SerikovAleksey/GPS-Tracker/Инструкция/1.jpg

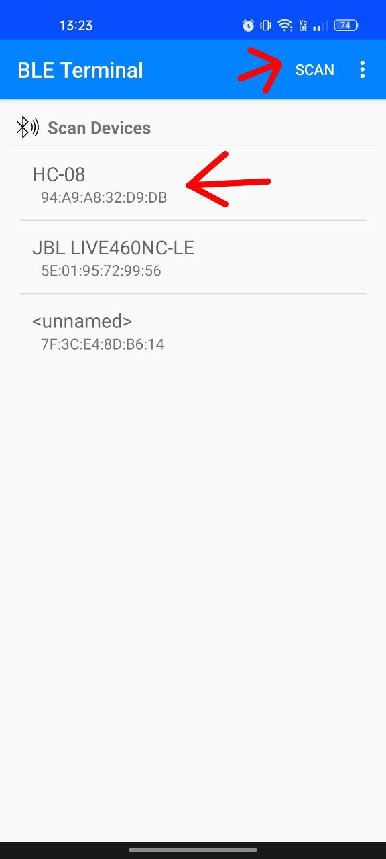
Инструкция/1.jpg
