SerikovAleksey/GPS-Tracker/Инструкция/2.jpg

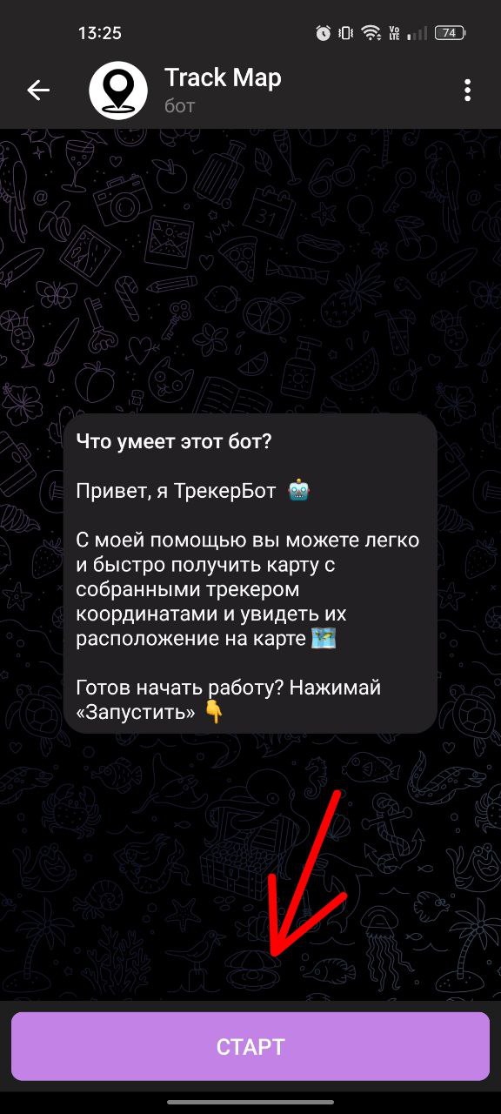
Инструкция/2.jpg
