SerikovAleksey/GPS-Tracker/Инструкция/4.jpg

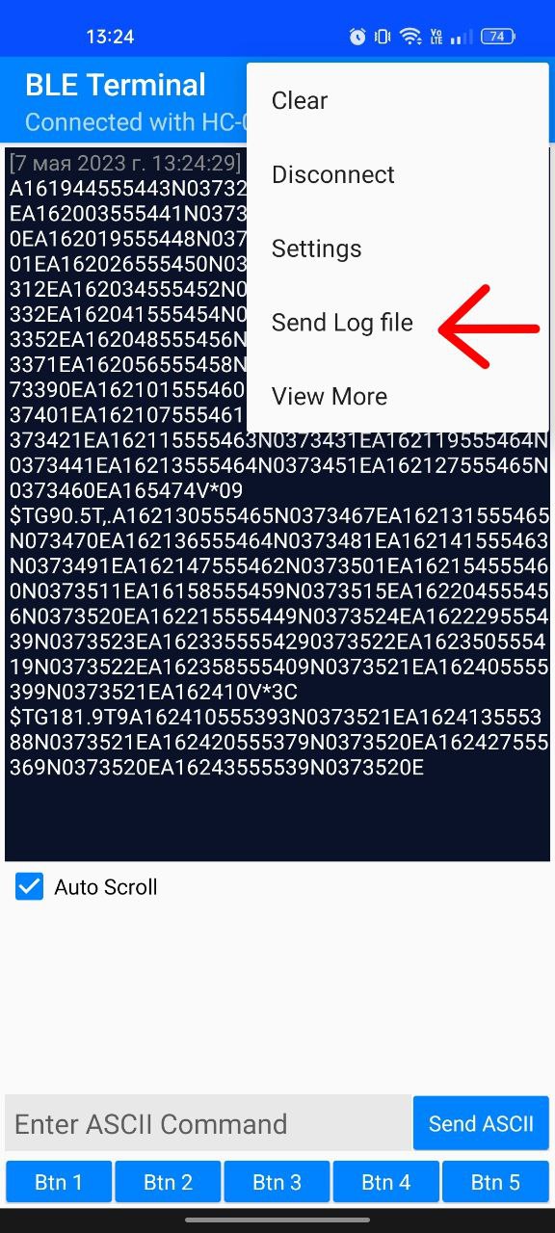
Инструкция/4.jpg
