SerikovAleksey/GPS-Tracker/Инструкция/5.jpg

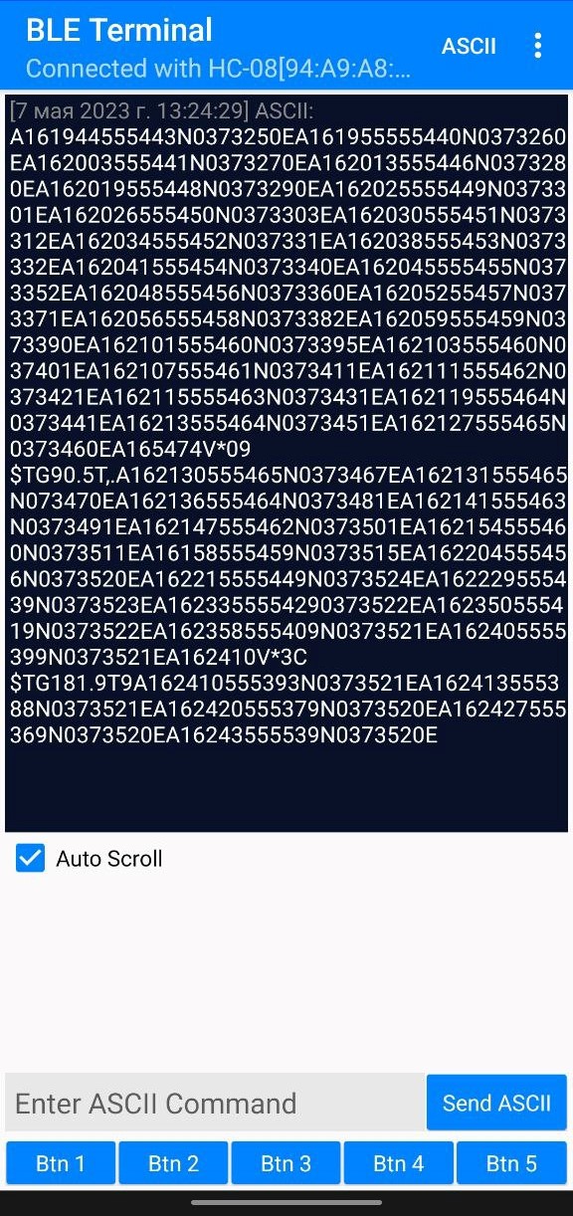
Инструкция/5.jpg
