SerikovAleksey/GPS-Tracker/Инструкция/6.jpg

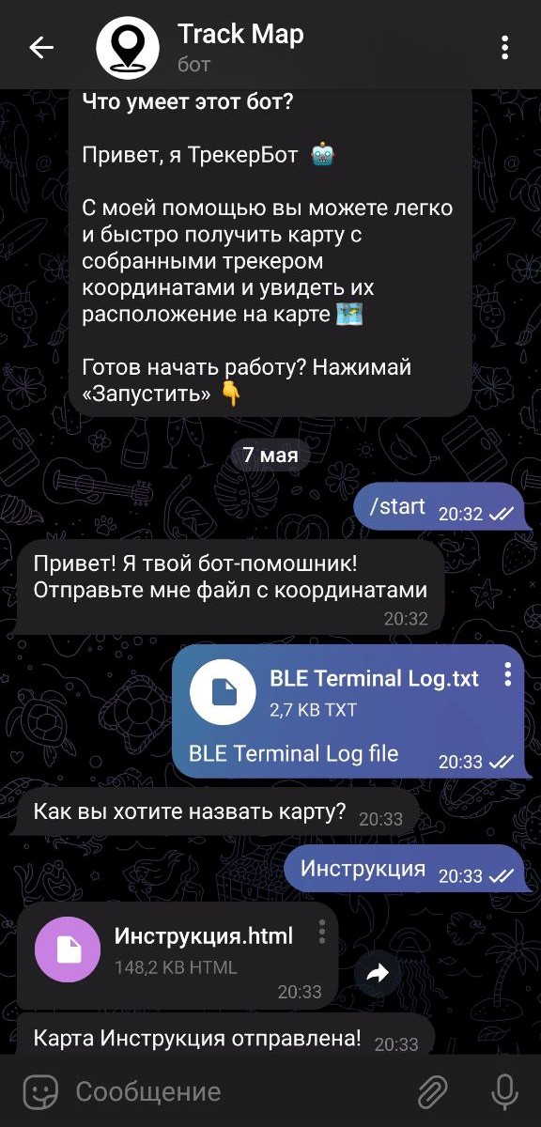
Инструкция/6.jpg
