SerikovAleksey/GPS-Tracker/Инструкция/трекер.png

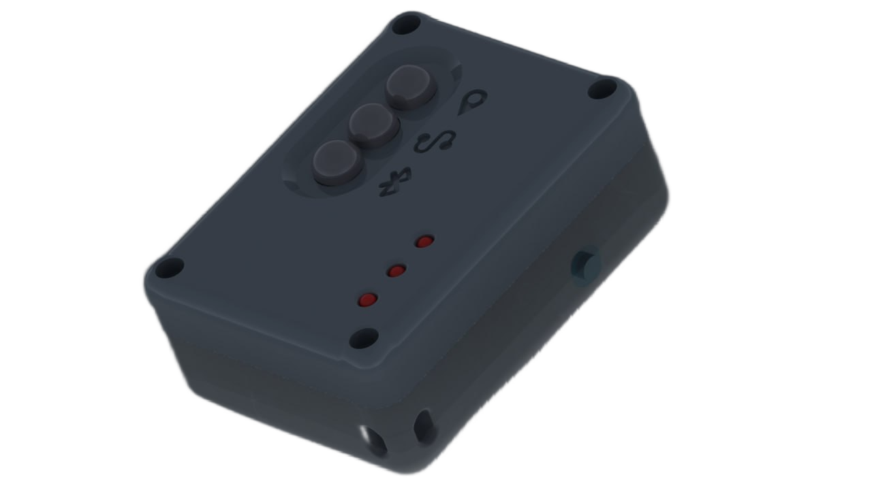
Инструкция/трекер.png
