SerikovAleksey/GPS-Tracker/Фото/photo_2023-04-14_23-05-25.jpg

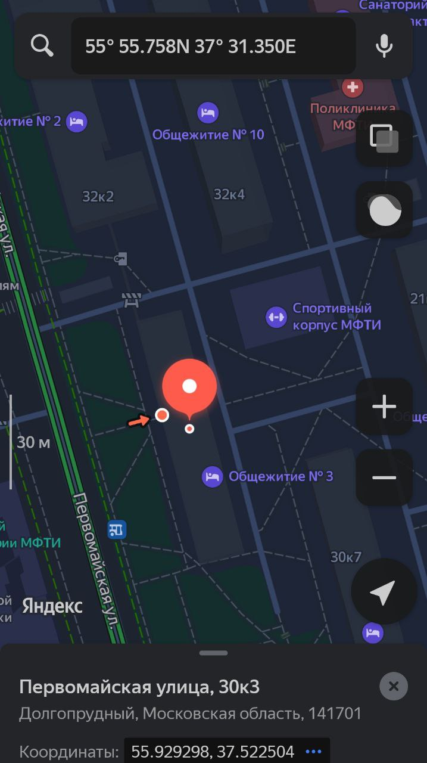
Фото/photo_2023-04-14_23-05-25.jpg
