SerikovAleksey/GPS-Tracker/Фото/трекер_3.jpg

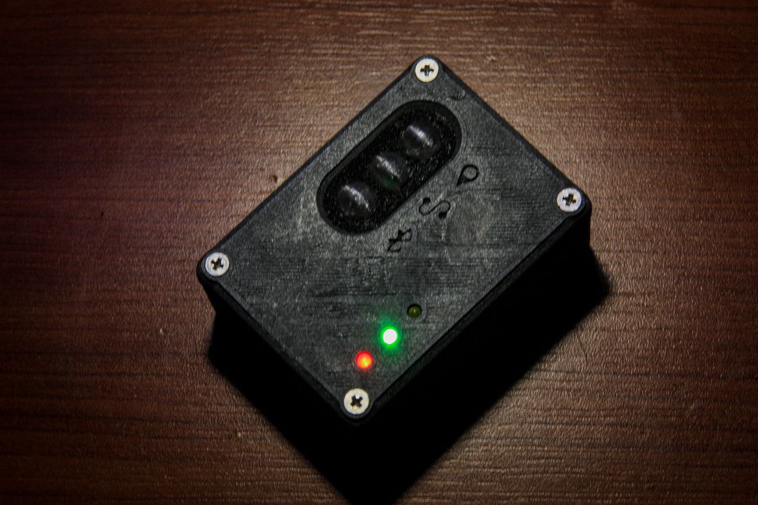
Фото/трекер_3.jpg
