SerikovAleksey/GPS-Tracker/Фото/трекер_4.jpg

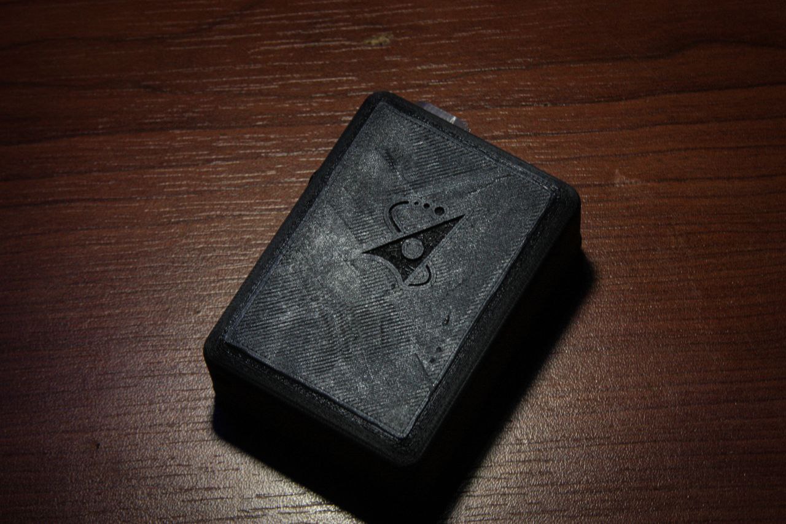
Фото/трекер_4.jpg
